shepherdingelectrons/ATtiny85Mario/TinyMario/bricks.h

static const unsigned char brick8x8[] PROGMEM= {0x77, 0x76, 0x75, 0x70, 0x77, 0x67, 0x57, 0x07};
static const unsigned char coin1[] PROGMEM= {0x3C, 0x7E, 0xE7, 0xFF, 0xFF, 0xFF, 0x7E, 0x3C};
static const unsigned char coin2[] PROGMEM= {0x00, 0x00, 0x7E, 0xCF, 0xFF, 0x7E, 0x00, 0x00};
static const unsigned char coin3[] PROGMEM= {0x00, 0x00, 0x00, 0x00, 0xFF, 0x00, 0x00, 0x00};
static const unsigned char block8x8[] PROGMEM= {0xFF, 0x81, 0xBD, 0x85, 0x85, 0x85, 0x81, 0xFF};
//static const unsigned char grass8x8[] PROGMEM= {0x07, 0x1F, 0x7F, 0x07, 0x1F, 0x3F, 0x0F, 0x07};
static const unsigned char topbrick[] PROGMEM={0x77, 0x77, 0x77, 0x77, 0x77, 0x67, 0x57, 0x07};
