shepherdingelectrons/ATtiny85Mario/TinyMario/mario_tiles.h

/*static const unsigned char mario_pipe[]  PROGMEM= {
  0xFF, 0xFF, 0x01, 0xE0, 0x01, 0xE0, 0x01, 0xE0, 0x01, 0xE0, 0xFF, 0xFF,
  0x02, 0x60, 0x02, 0x60, 0x02, 0x60, 0x02, 0x60, 0x02, 0x60, 0x02, 0x60,
  0xFC, 0x3F, 0x02, 0x60, 0x02, 0x60, 0x02, 0x60,
};*/

static const unsigned char mario_pipe2[] PROGMEM= {
	63, 0, 255, 239, 255, 255, 33, 16, 33, 16, 33, 16, 33, 16, 33, 16, 33, 16, 33, 16, 33, 16, 33, 16, 33, 16, 33, 16, 225, 239, 63, 0};
